kj-49/path-pilot/firmware/path-pilot.X/communication.c

#include <avr/io.h>
#include <string.h>

#include "communication.h"
#include "avr-common.h"


#define BAUD_RATE_CALC(BAUD_RATE) ((float)(64 * 1000000 / (16 * (float)BAUD_RATE)) + 0.5)


void usart_init() {
    // Set PIND7 to output
    PORTD.DIRSET |= (1 << USART_D_IN_PIN);
    
    USART1.BAUD = (uint16_t)(9600);
    
    // Set the mode to synchronous and data format to 8-bit
    USART1.CTRLC = 0b10000011;
    USART1.CTRLC = 0b10000011;
    
    // Enable transmission
    USART1.CTRLB |= (1 << 6);                      
}

void usart_send_str(const char *str) {
    for(size_t i = 0; i < strlen(str); i++)    
    {        
        usart_send_char(str[i]);    
    }
}


void usart_send_char(char c) {
    if (!DEBUGGING) {
        return;
    }
    // Wait until the register is ready for new data (pg. 377 of DS)
    while(!(USART1.STATUS & (1 << 5)))
    {
        ;
    }
    
    USART1.TXDATAL = c;
}

void u_println(const char *str) {
    usart_send_str(str);
    usart_send_char('\n');
}
